RICCIARDI-Adrien/Chip8_Console/Software/Sources/Video_Player.c

/** @file Video_Player.c
 * See Video_Player.h for description.
 * @author Adrien RICCIARDI
 */
#include <Display.h>
#include <FAT.h>
#include <Keyboard.h>
#include <Localized_String.h>
#include <Log.h>
#include <NCO.h>
#include <SD_Card.h>
#include <Shared_Buffer.h>
#include <string.h>
#include <Video_Player.h>
#include <xc.h>

//-------------------------------------------------------------------------------------------------
// Private constants
//-------------------------------------------------------------------------------------------------
/** Set to 1 to enable the log messages, set to 0 to disable them. */
#define VIDEO_PLAYER_IS_LOGGING_ENABLED 1

//-------------------------------------------------------------------------------------------------
// Private functions
//-------------------------------------------------------------------------------------------------
// TODO
static inline unsigned char VideoPlayerFindFile(char *Pointer_String_File_Name, TFATFileDescriptor *Pointer_File_Descriptor)
{
	TFATFileInformation File_Information;

	// Begin listing the files
	if (FATListStart("/") != 0)
	{
		LOG(VIDEO_PLAYER_IS_LOGGING_ENABLED, "FATListStart() failed.");
		return 1;
	}

	// Search for the video file
	while (FATListNext(&File_Information) == 0)
	{
		LOG(VIDEO_PLAYER_IS_LOGGING_ENABLED, "File found : name=\"%s\", is directory=%u, size=%lu, first cluster=%lu.",
			File_Information.String_Short_Name,
			File_Information.Is_Directory,
			File_Information.Size,
			File_Information.First_Cluster_Number);

		// We are searching for a file, discard any directory
		if (File_Information.Is_Directory)
		{
			LOG(VIDEO_PLAYER_IS_LOGGING_ENABLED, "This is a directory, skipping it.");
			continue;
		}

		// Is this the searched file ?
		if (strcmp((char *) File_Information.String_Short_Name, Pointer_String_File_Name) == 0)
		{
			LOG(VIDEO_PLAYER_IS_LOGGING_ENABLED, "Found the video file.");
			FATReadSectorsStart(&File_Information, Pointer_File_Descriptor);
			return 0;
		}
	}

	LOG(VIDEO_PLAYER_IS_LOGGING_ENABLED, "No video file found.");
	return 1;
}

//-------------------------------------------------------------------------------------------------
// Public functions
//-------------------------------------------------------------------------------------------------
void VideoPlayer(void)
{
	TFATFileDescriptor File_Descriptor;

	// Retrieve the movie file to play
	if (VideoPlayerFindFile("VIDEO.BIN", &File_Descriptor) != 0)
	{
		LOG(VIDEO_PLAYER_IS_LOGGING_ENABLED, "No video file found.");
		DisplayDrawTextMessage(Shared_Buffer_Display, LocalizedStringGet(LOCALIZED_STRING_ID_SD_CARD_MESSAGE_TITLE), LocalizedStringGet(LOCALIZED_STRING_ID_SD_CARD_MESSAGE_NO_VIDEO_FILE_FOUND_ERROR_CONTENT));
		while (!KeyboardIsMenuKeyPressed());
		return;
	}

	// Wait for tick start to synchronize the first frame rendering
	NCO_CLEAR_TICK_INTERRUPT_FLAG();
	while (!NCO_IS_TICK_ELAPSED());

	// Read the whole file until the end if reached or the user exited
	while (FATReadSectorsNext(&File_Descriptor, sizeof(Shared_Buffer_Display) / SD_CARD_BLOCK_SIZE, Shared_Buffers.Buffer) == 0) // Read a full frame at a time, its size is a power of the block size so no rounding error can happen
	{
		// Check on each frame if the user wants to exit
		if (KeyboardIsMenuKeyPressed())
		{
			LOG(VIDEO_PLAYER_IS_LOGGING_ENABLED, "User has quit.");
			return;
		}

		// Display the next frame
		DisplayDrawFullSizeBuffer(Shared_Buffers.Buffer);

		// Wait for the next tick to keep the frame rate stable
		while (!NCO_IS_TICK_ELAPSED());
		NCO_CLEAR_TICK_INTERRUPT_FLAG();
	}
}
