RICCIARDI-Adrien/Chip8_Console/Software/Includes/Video_Player.h

/** @file Video_Player.h
 * Play proprietary video files from the SD card.
 * @author Adrien RICCIARDI
 */
#ifndef H_VIDEO_PLAYER_H
#define H_VIDEO_PLAYER_H

/** Allow the user to choose a video file then play it. */
void VideoPlayer(void);

#endif
